Gearlux/ArduinoWordClock/userinterface/userinterface_bb.png

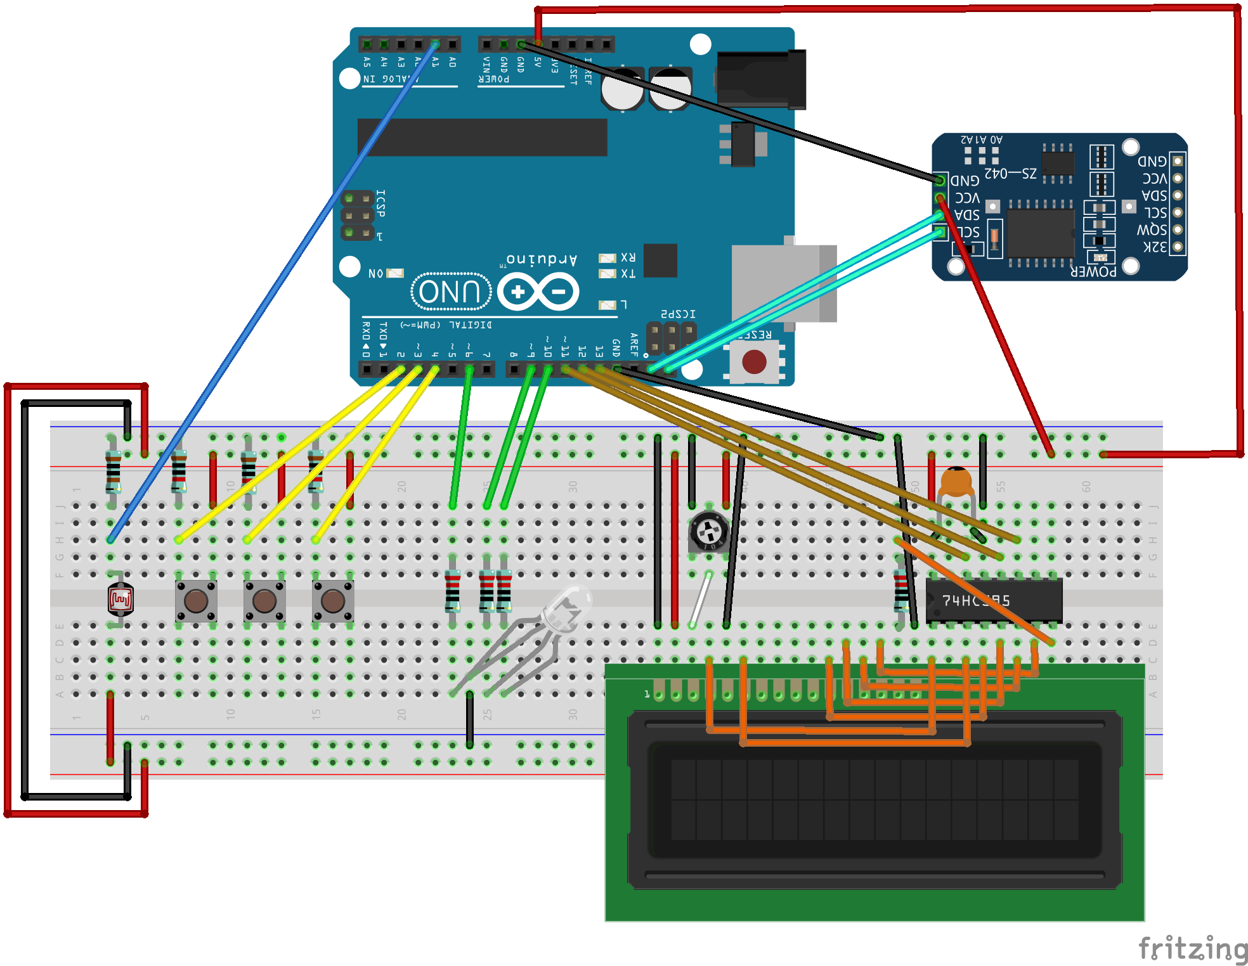
userinterface/userinterface_bb.png
